wonbinbk/SSS/Data/NoPIDwithstepResponse.png

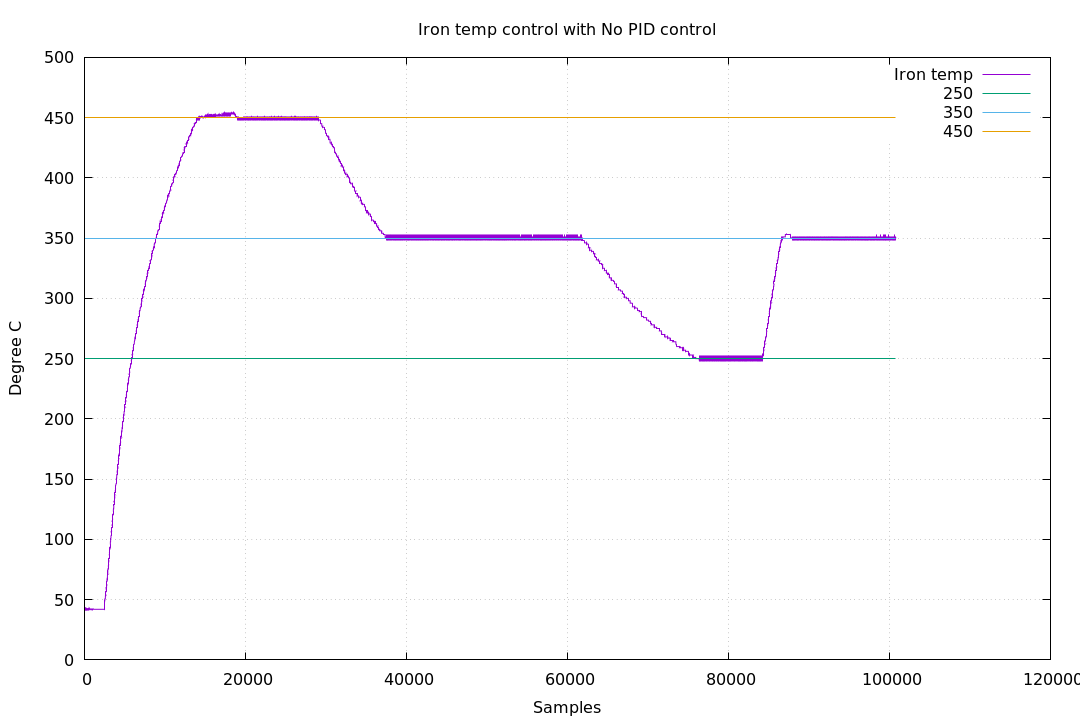
Data/NoPIDwithstepResponse.png
