wonbinbk/SSS/Data/P50I0D0.png

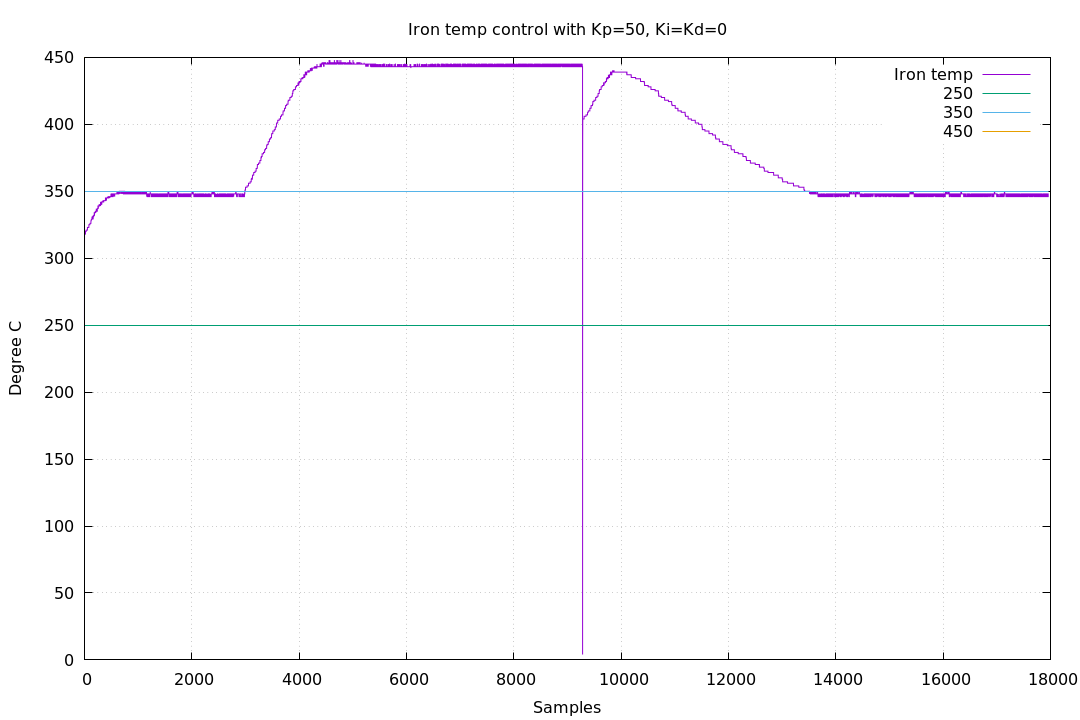
Data/P50I0D0.png
