wonbinbk/SSS/Data/P50I10D20.png

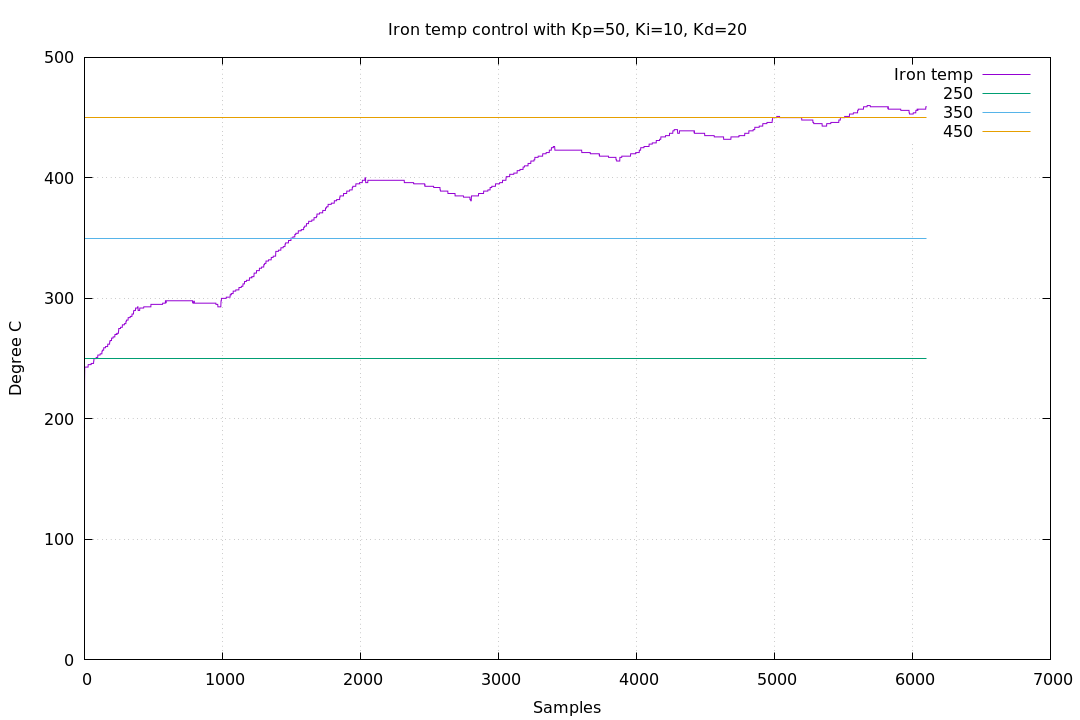
Data/P50I10D20.png
