wonbinbk/SSS/Data/P100I0D50.png

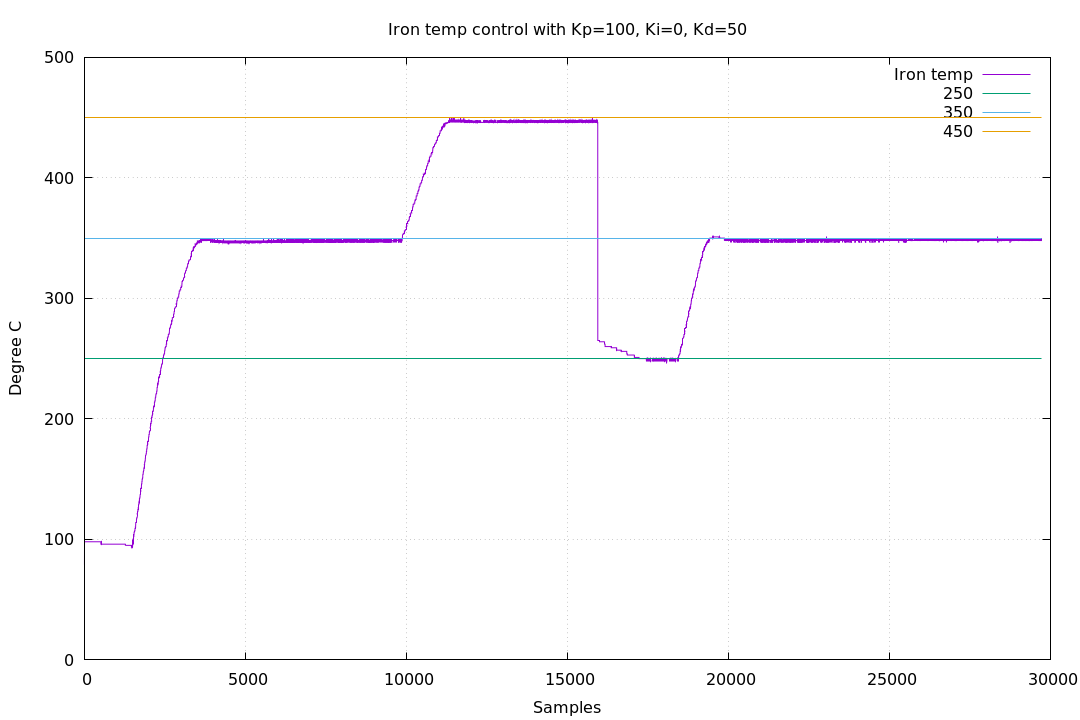
Data/P100I0D50.png
