wonbinbk/SSS/Data/P100I5D50.png

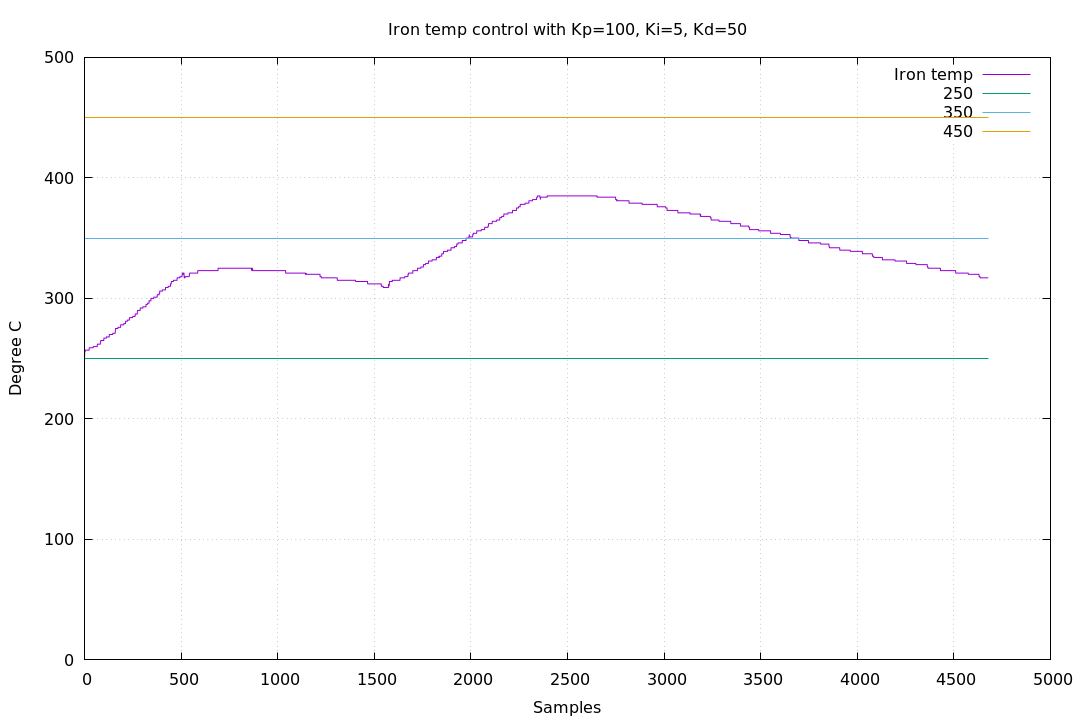
Data/P100I5D50.png
