wonbinbk/SSS/Data/P100I50D50.png

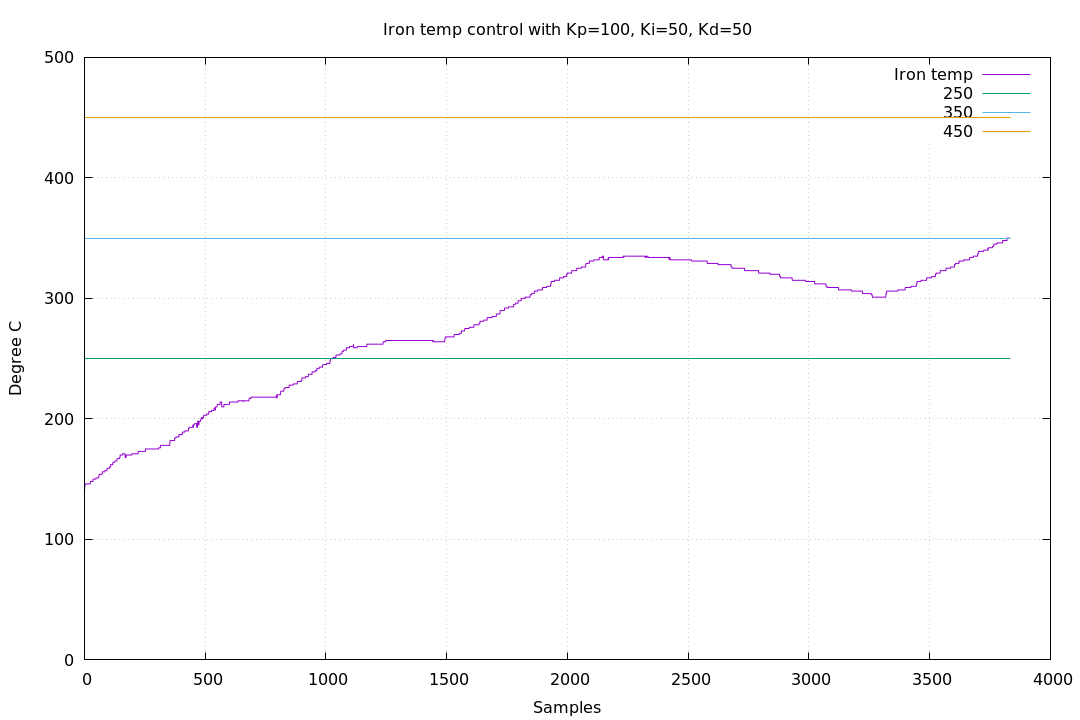
Data/P100I50D50.png
