wonbinbk/SSS/Data/P300I0D0.png

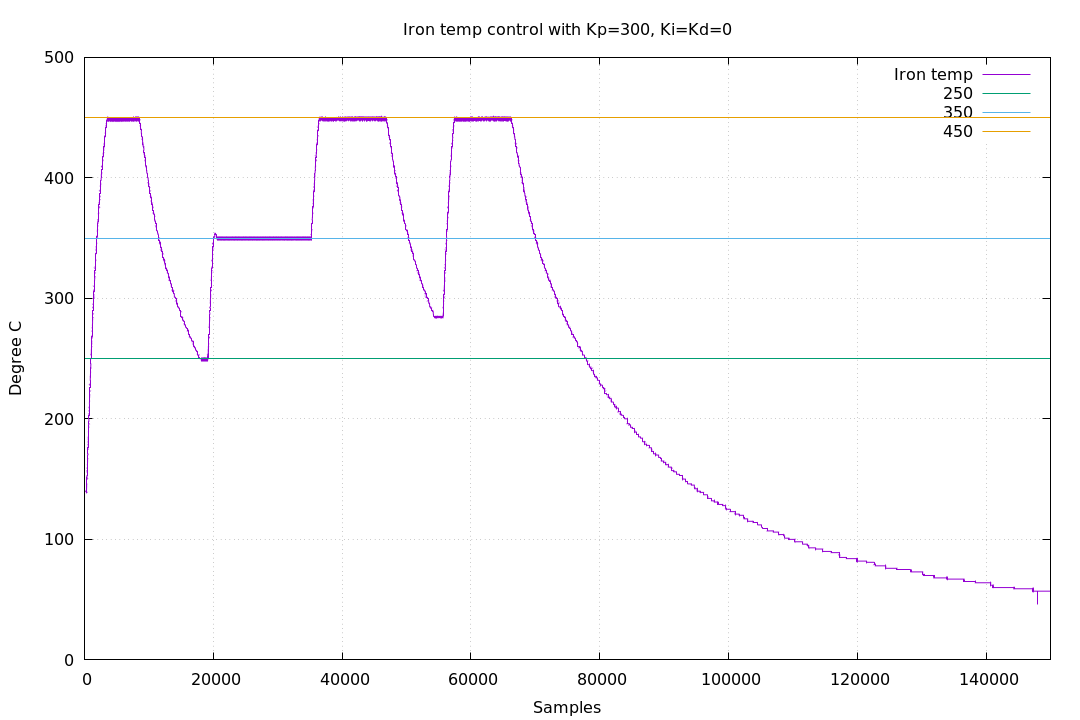
Data/P300I0D0.png
