wonbinbk/SSS/Data/P300I0D100.png

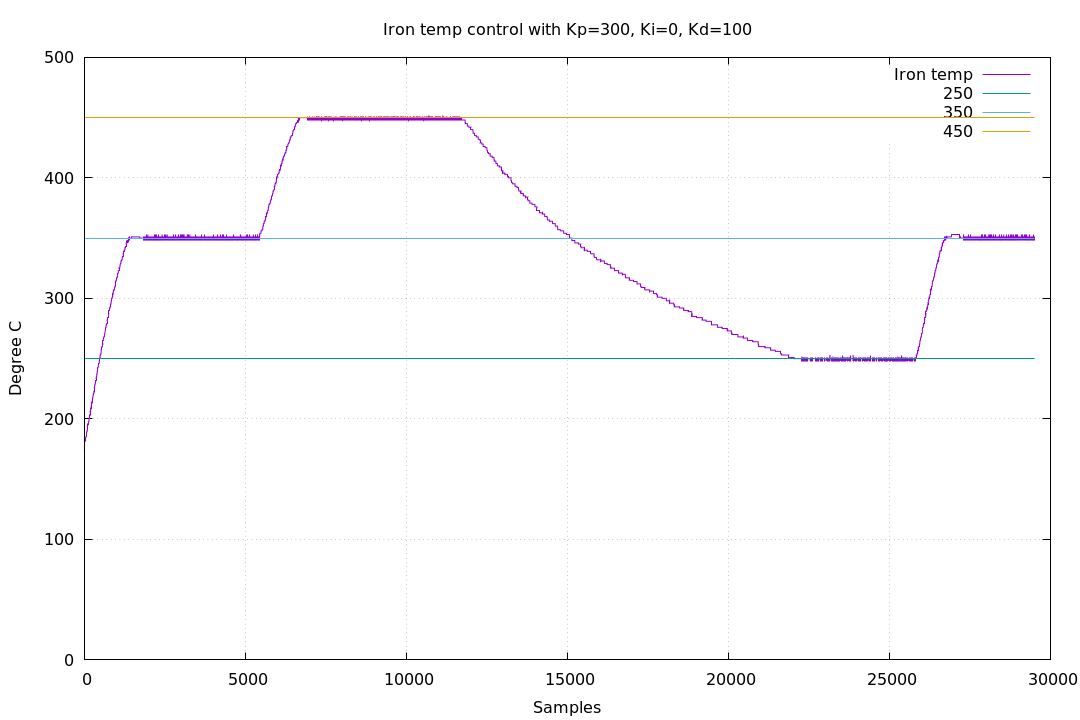
Data/P300I0D100.png
