wonbinbk/SSS/Data/P300I10D0.png

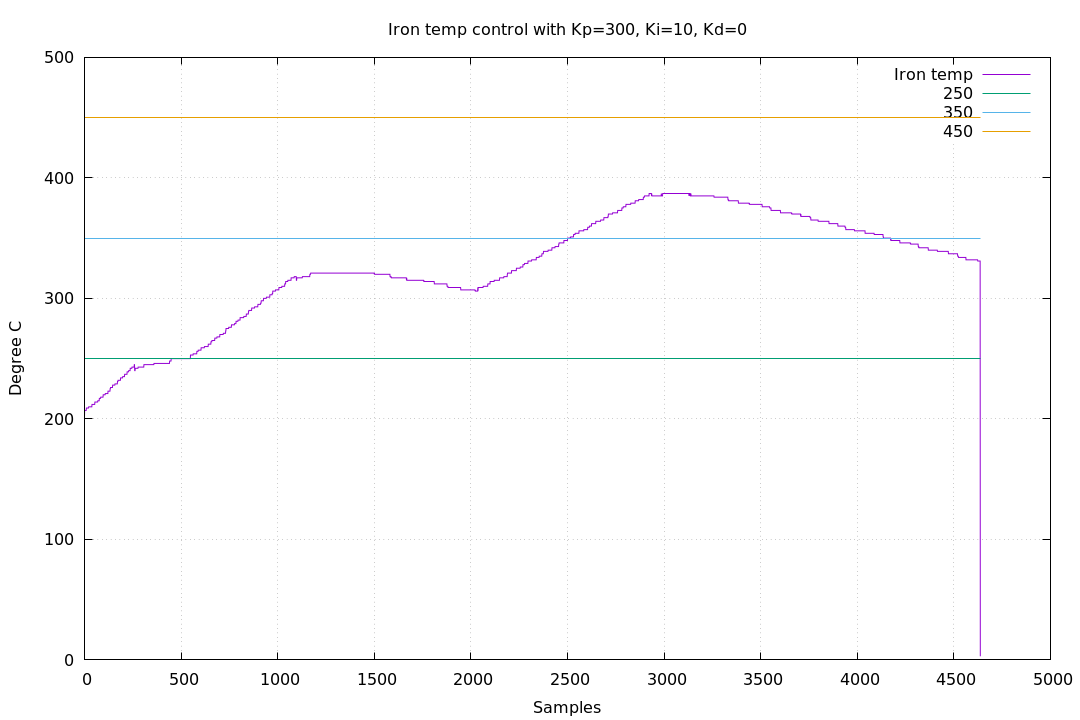
Data/P300I10D0.png
