wonbinbk/SSS/Data/P300I100D0.png

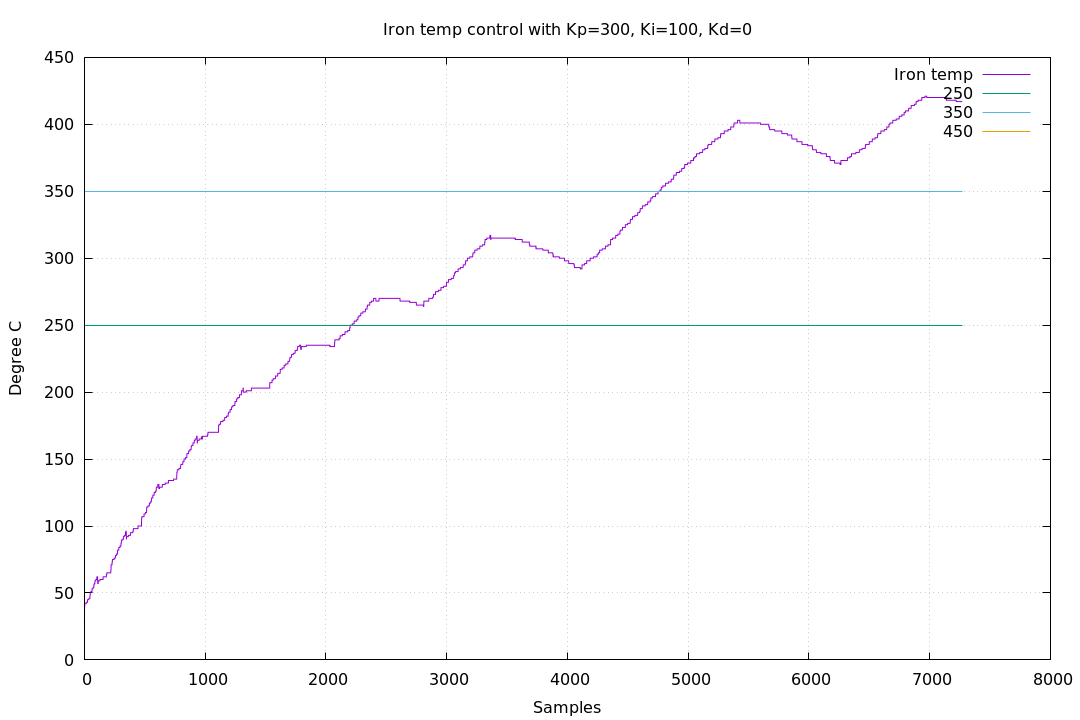
Data/P300I100D0.png
