wonbinbk/SSS/Data/P500I0D0.png

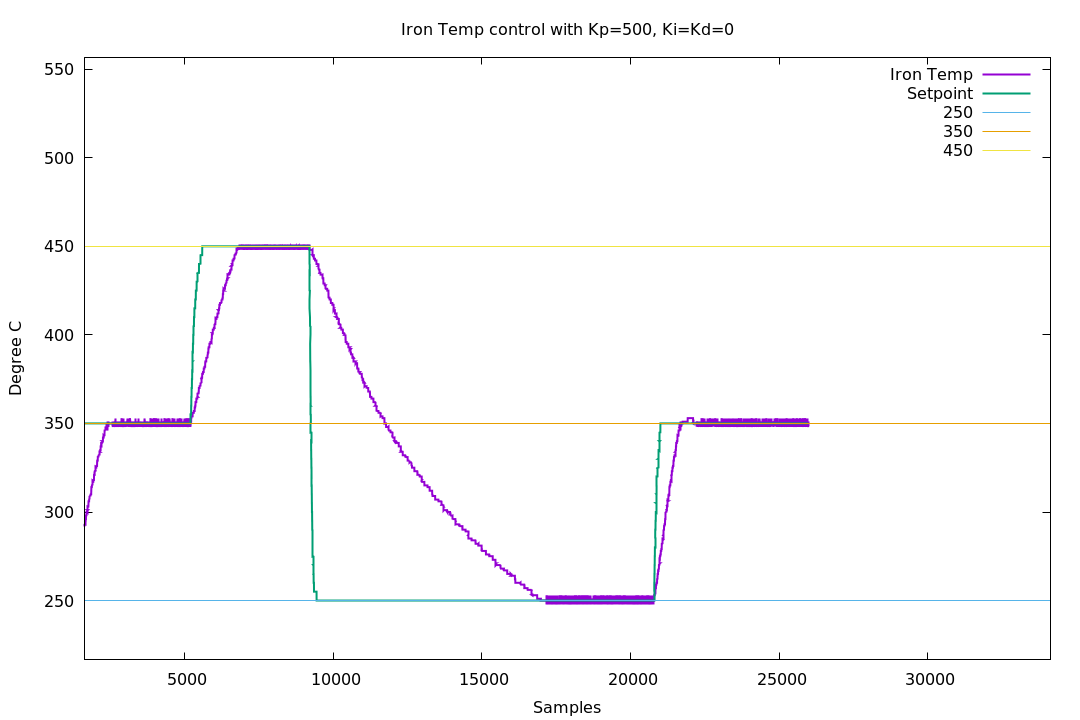
Data/P500I0D0.png
